stonetronics/stepperpi/pcb/stepperpi/3D/raspberry/Female USB Type C Connector, RPi4ModelB.SLDPRT

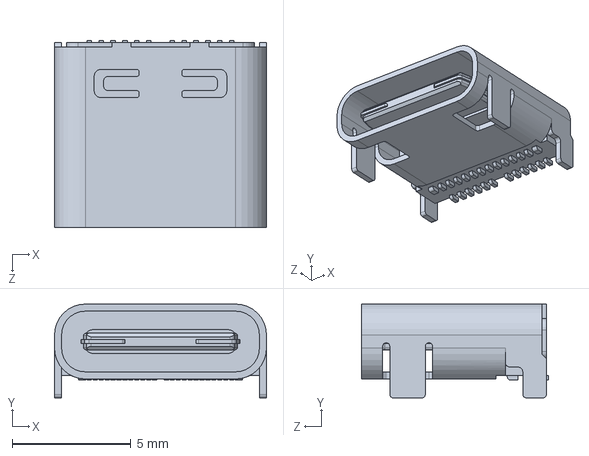
[picture p14: CAD file, 2025-04-23]
pcb/stepperpi/3D/raspberry/Female USB Type C Connector, RPi4ModelB.SLDPRT
8.94 x 3.96 x 7.90 mm
