stonetronics/stepperpi/pcb/stepperpi/3D/raspberry/2X USB2.0 PORTS, RPi4ModelB.SLDPRT

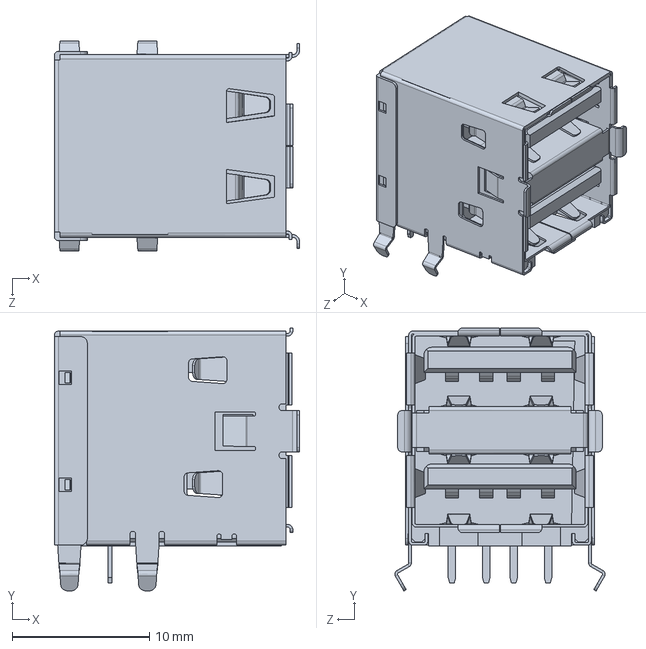
[picture p15: CAD file, 2025-04-23]
pcb/stepperpi/3D/raspberry/2X USB2.0 PORTS, RPi4ModelB.SLDPRT
17.9 x 19.2 x 15.3 mm
