stonetronics/stepperpi/pcb/stepperpi/3D/raspberry/Female Micro HDMI Connector, RPi4ModelB.SLDPRT

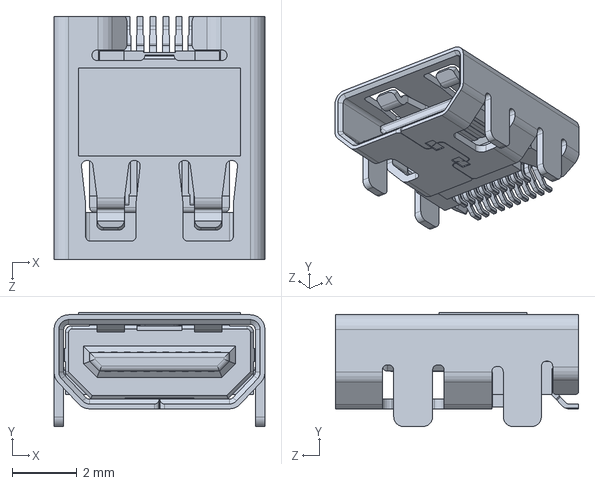
[picture p17: CAD file, 2025-04-23]
pcb/stepperpi/3D/raspberry/Female Micro HDMI Connector, RPi4ModelB.SLDPRT
6.50 x 3.52 x 7.50 mm
