stonetronics/stepperpi/pcb/stepperpi/3D/raspberry/Cypress CYW43455 Wireless Module Cover, RPi4ModelB.SLDPRT

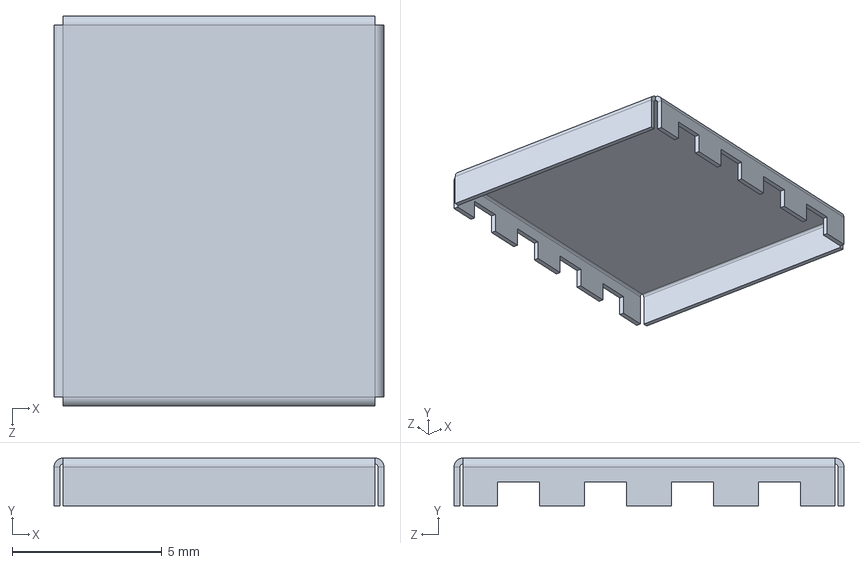
[picture p18: CAD file, 2025-04-23]
pcb/stepperpi/3D/raspberry/Cypress CYW43455 Wireless Module Cover, RPi4ModelB.SLDPRT
11.0 x 1.60 x 13.0 mm
