stonetronics/stepperpi/pcb/stepperpi/3D/A4988/C1206B.SLDPRT

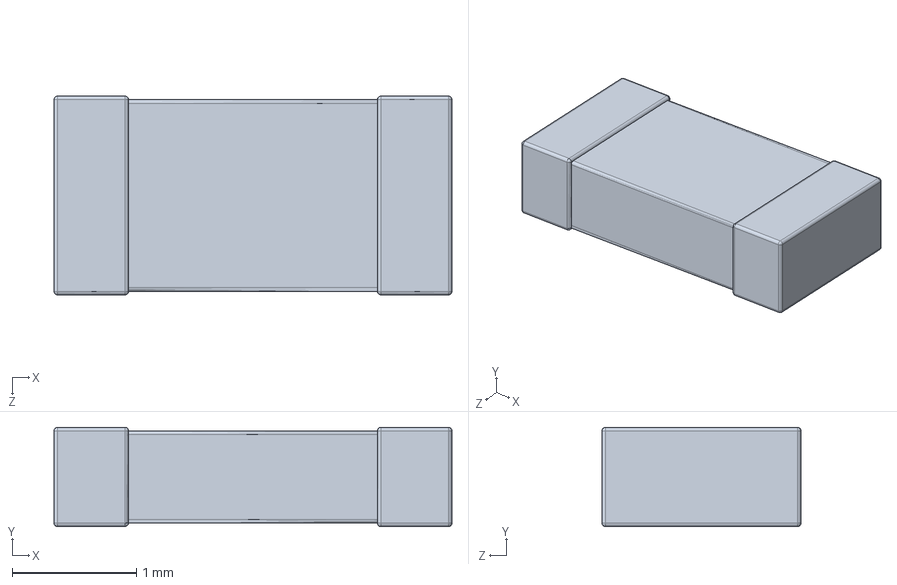
[picture p19: CAD file, 2025-04-23]
pcb/stepperpi/3D/A4988/C1206B.SLDPRT
3.20 x 0.8 x 1.60 mm
