stonetronics/stepperpi/pcb/stepperpi/3D/A4988/C0402.SLDPRT

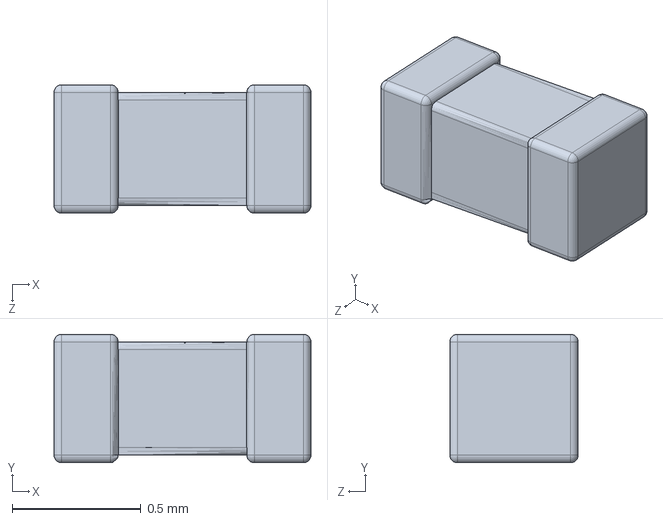
[picture p20: CAD file, 2025-04-23]
pcb/stepperpi/3D/A4988/C0402.SLDPRT
1.00 x 0.5 x 0.5 mm
